lukasznowarkiewicz/HSSmartModule/images/HSSM-3d-model-bottom.png

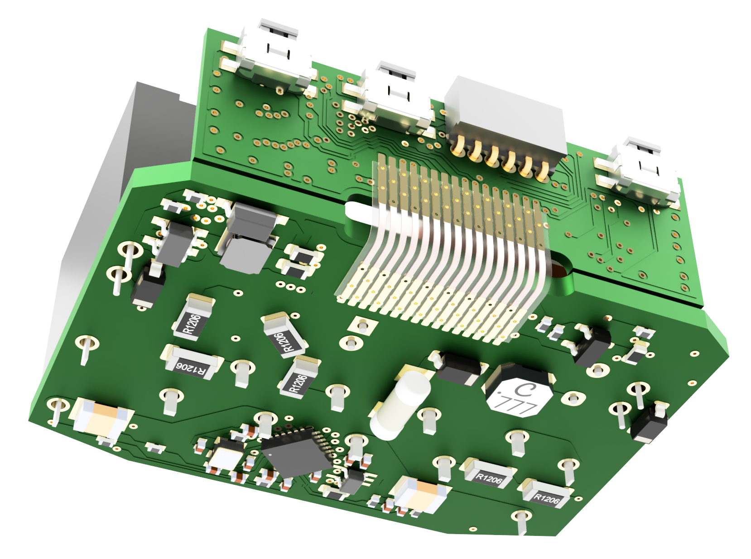
images/HSSM-3d-model-bottom.png
