lukasznowarkiewicz/HSSmartModule/images/HSSM-3d-model-top.png

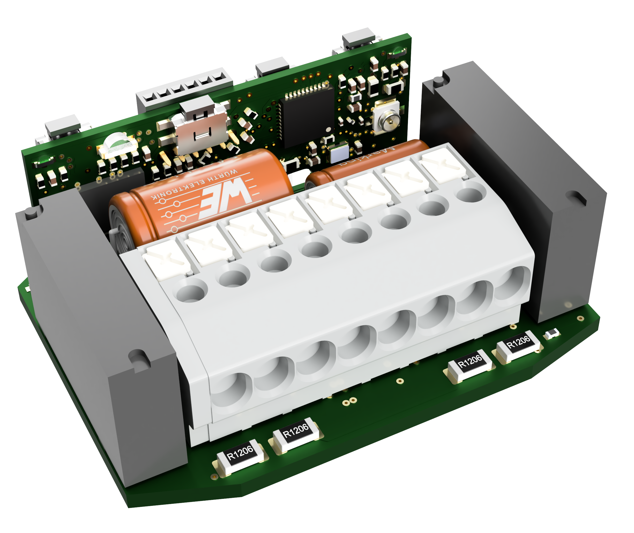
images/HSSM-3d-model-top.png
