lukasznowarkiewicz/HSSmartModule/images/HSSM-FCB-PCB-BOTTOM.png

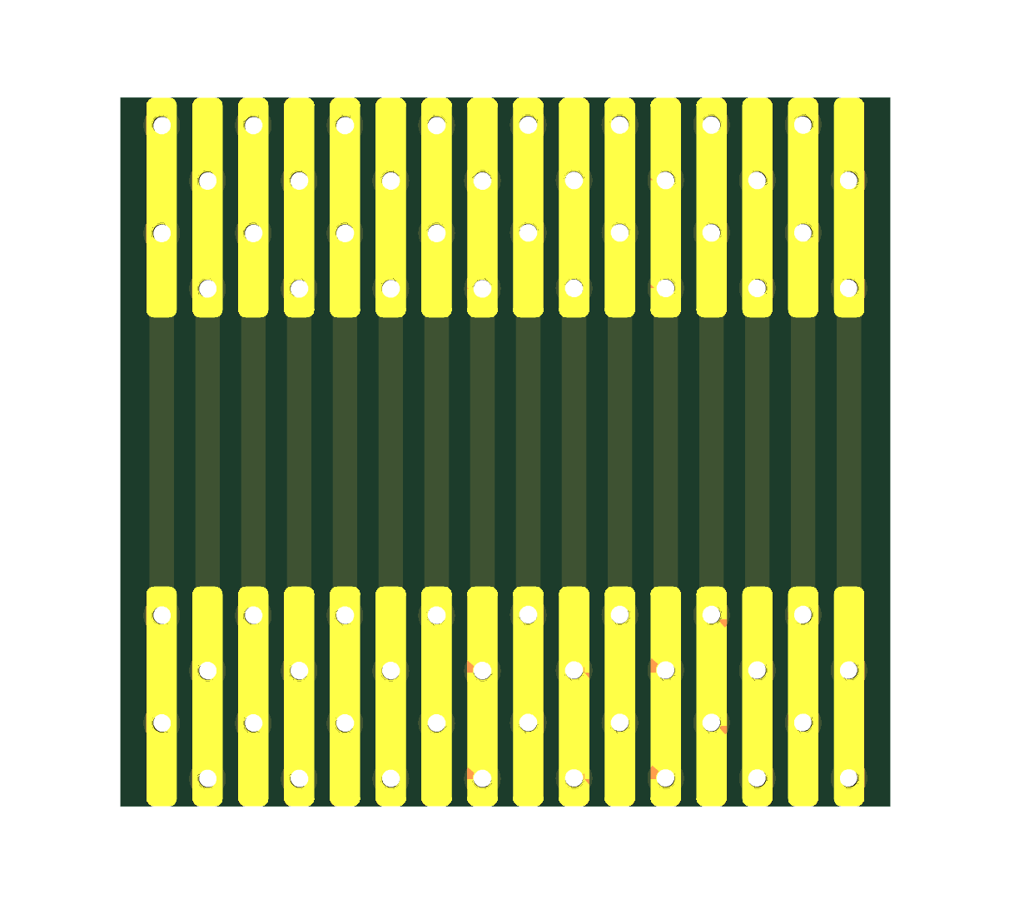
images/HSSM-FCB-PCB-BOTTOM.png
