lukasznowarkiewicz/HSSmartModule/images/HSSM-FCB-PCB-TOP.png

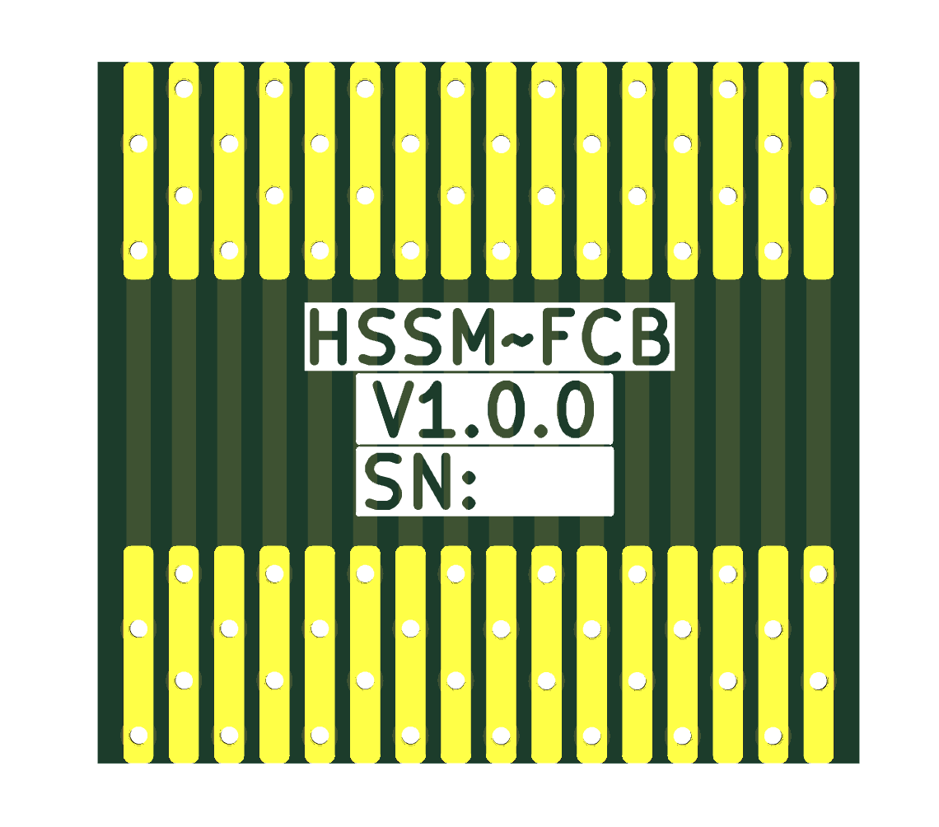
images/HSSM-FCB-PCB-TOP.png
