lukasznowarkiewicz/HSSmartModule/images/HSSM-HVPCB-PCB-BOTTOM-IZO.png

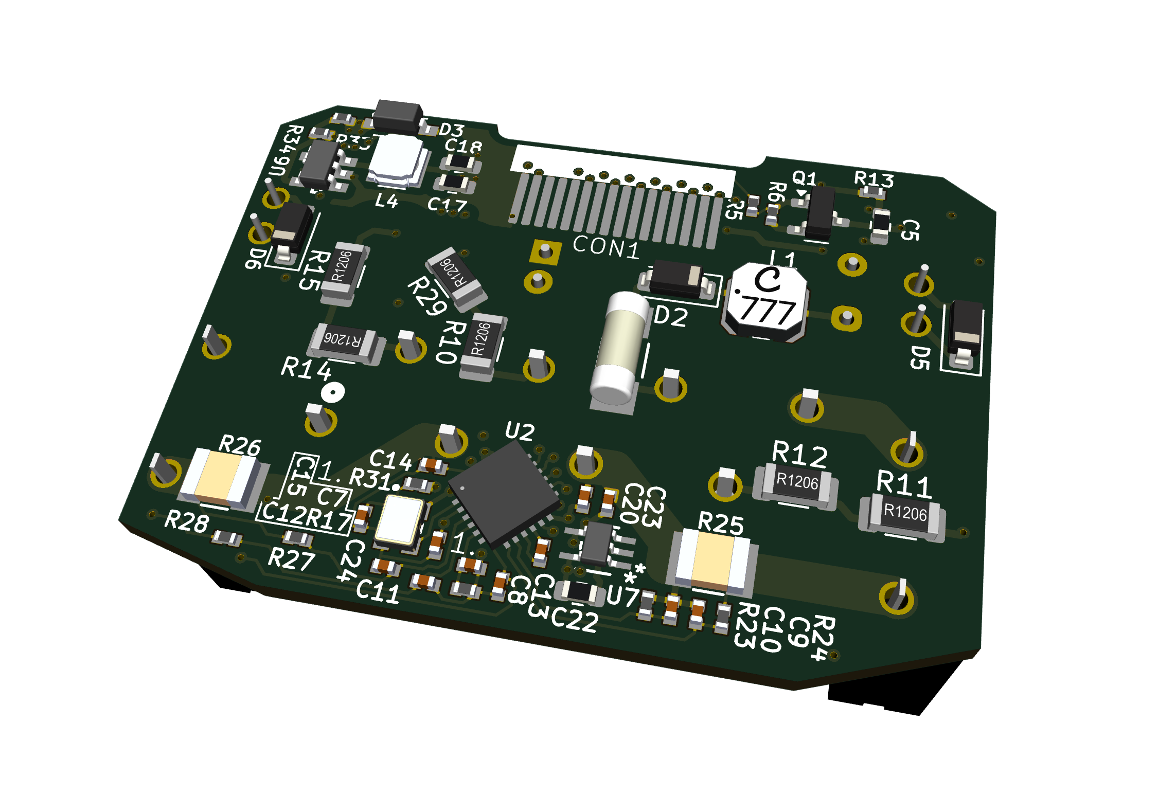
images/HSSM-HVPCB-PCB-BOTTOM-IZO.png
