lukasznowarkiewicz/HSSmartModule/images/HSSM-HVPCB-PCB-TOP-IZO2.png

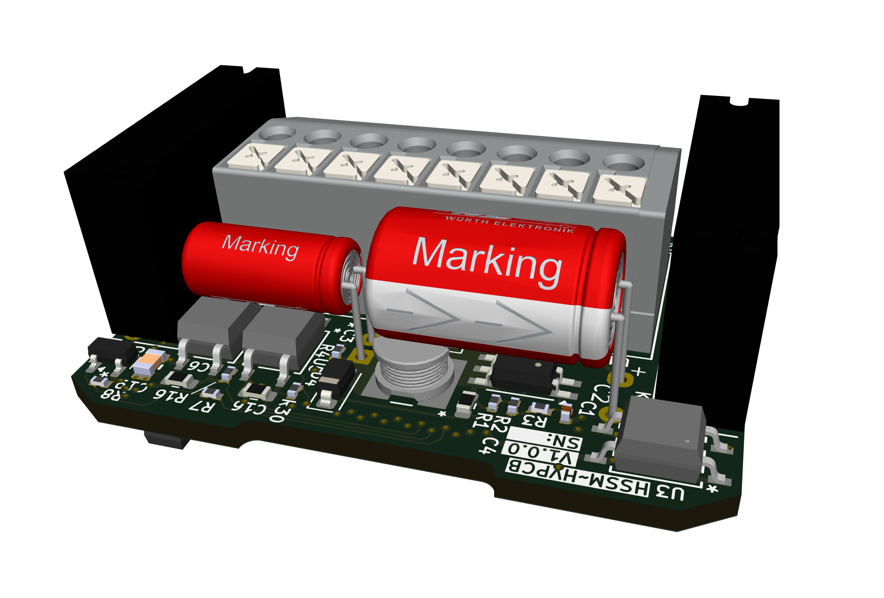
images/HSSM-HVPCB-PCB-TOP-IZO2.png
