lukasznowarkiewicz/HSSmartModule/images/HSSM-HVPCB-PCB-TOP-IZO.png

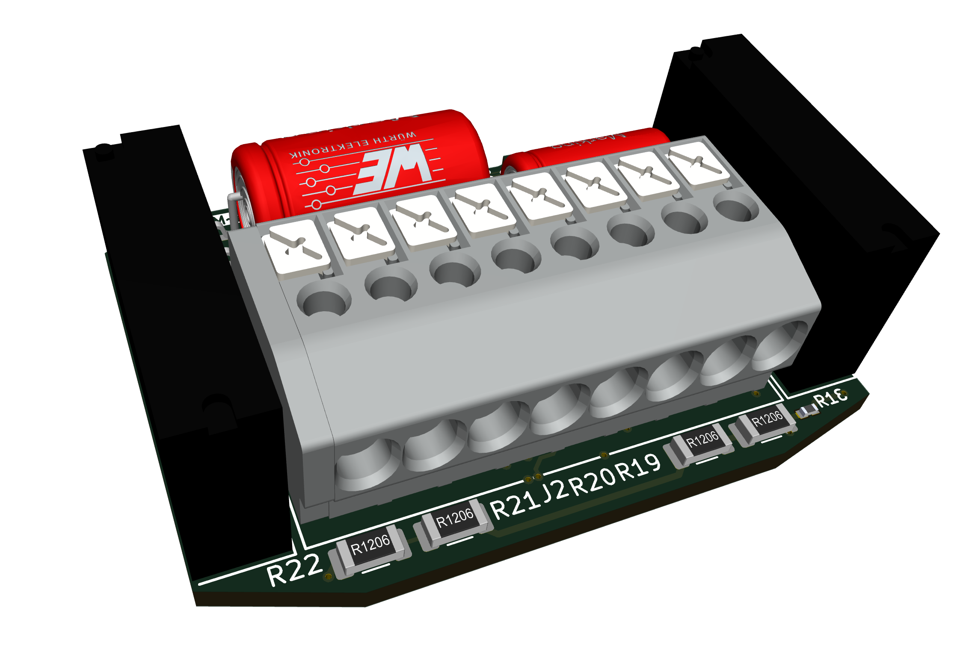
images/HSSM-HVPCB-PCB-TOP-IZO.png
